Xinyuan-LilyGO/LilyGo-T-Relay/image/T-Relay8.jpg

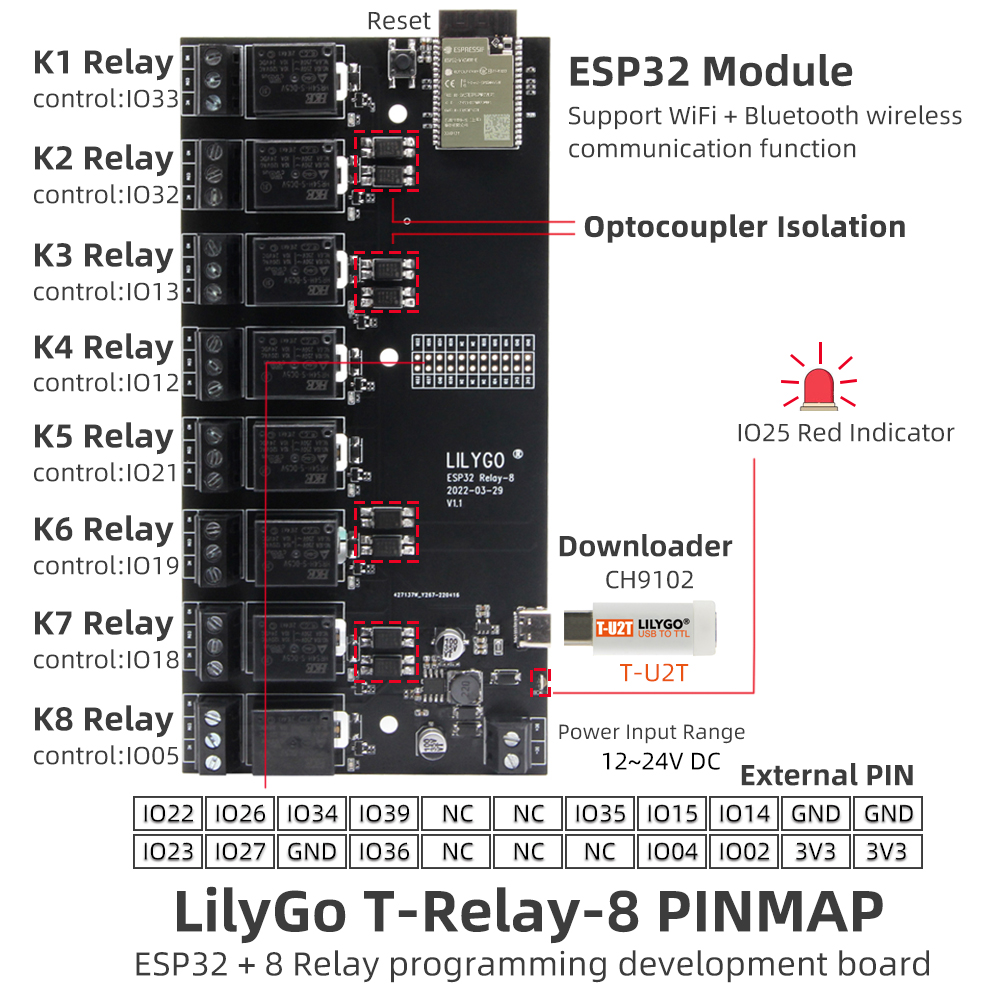
image/T-Relay8.jpg
