Xinyuan-LilyGO/LilyGo-T-Relay/examples/T-Relay-4-ESP32/w5500_esplib_v3.0/pin_config.h

/*
 * @Description: None
 * @version: None
 * @Author: None
 * @Date: 2023-06-05 13:01:59
 * @LastEditors: LILYGO_L
 * @LastEditTime: 2023-07-21 18:55:52
 */
#pragma once

/*ESP32S3*/
#define PIN_LCD_BL 38

#define PIN_LCD_D0 39
#define PIN_LCD_D1 40
#define PIN_LCD_D2 41
#define PIN_LCD_D3 42
#define PIN_LCD_D4 45
#define PIN_LCD_D5 46
#define PIN_LCD_D6 47
#define PIN_LCD_D7 48

#define PIN_POWER_ON 15

#define PIN_LCD_RES 5
#define PIN_LCD_CS 6
#define PIN_LCD_DC 7
#define PIN_LCD_WR 8
#define PIN_LCD_RD 9

#define PIN_BUTTON_1 0
#define PIN_BUTTON_2 14
#define PIN_BAT_VOLT 4

#define PIN_IIC_SCL 17
#define PIN_IIC_SDA 18

#define PIN_TOUCH_INT 16
#define PIN_TOUCH_RES 21

/* External expansion */
// SD
#define PIN_SD_CS 16
#define PIN_SD_CLK 21
#define PIN_SD_MISO 3
#define PIN_SD_MOSI 10

// MPR121_PIN
#define MPR121_ADDR1 0x5A
#define MPR121_ADDR2 0x5B // VCC
#define MPR121_IRQ_PIN 2
#define MPR121_SDA 18
#define MPR121_SCL 17

// PCF8575_PIN
#define T_DISPLAY_PCF8575_IIC_ADDRESS 0x20
#define PCF8575_IRQ_PIN 2
#define PCF8575_SDA 18
#define PCF8575_SCL 17
#define T_DISPLAY_PCF8575_INTERRUPTPIN 2

// PCM5102A_PIN
#define PCM5102A_LRCK 13
#define PCM5102A_DIN 12
#define PCM5102A_BCK 11

// XL95x5_PIN
#define T_DISPLAY_XL95x5_IIC_ADDRESS 0X20
#define T_DISPLAY_XL95x5_SDA 18 // Default configuration
#define T_DISPLAY_XL95x5_SCL 17
#define T_DISPLAY_XL95x5_INTERRUPTPIN 2

// W5500_PIN
#define PIN_W5500_CLK 22
#define PIN_W5500_MISO 13 // LilyGo-T-Relay-4
// #define PIN_W5500_MISO 34 // LilyGo-T-Relay-8
#define PIN_W5500_MOSI 26
#define PIN_W5500_CS 27
#define PIN_W5500_RESET 23
#define PIN_W5500_INT 36

// LilyGo-T-Relay-4
#define RELAY4_PIN_1 21
#define RELAY4_PIN_2 19
#define RELAY4_PIN_3 18
#define RELAY4_PIN_4 5
#define LED_PIN 25

// LilyGo-T-Relay-8
#define RELAY8_PIN_1 33
#define RELAY8_PIN_2 32
#define RELAY8_PIN_3 13
#define RELAY8_PIN_4 12
#define RELAY8_PIN_5 21
#define RELAY8_PIN_6 19
#define RELAY8_PIN_7 18
#define RELAY8_PIN_8 5
#define LED_PIN 25
