Xinyuan-LilyGO/LilyGo-T-Relay/examples/T-Relay-ESP32S3/NimBLE_Server/NimBLE_Server.ino

/**
 * @file      NimBLE_Server.ino
 * @author    Lewis He (lewishe@outlook.com)
 * @license   MIT
 * @copyright Copyright (c) 2023  Shenzhen Xin Yuan Electronic Technology Co., Ltd
 * @date      2023-02-27
 *
 */

#include <NimBLEDevice.h>
#include <ShiftRegister74HC595_NonTemplate.h>

#define DATA_PIN                    7
#define CLOCK_PIN                   5
#define LATCH_PIN                   6
#define ENABLE_PIN                  4       //EN Pin is only available in V1.1 version

ShiftRegister74HC595_NonTemplate *control = NULL;
static NimBLEServer *pServer;

/**  None of these are required as they will be handled by the library with defaults. **
 **                       Remove as you see fit for your needs                        */
class ServerCallbacks: public NimBLEServerCallbacks
{
    void onConnect(NimBLEServer *pServer)
    {
        Serial.println("Client connected");
        Serial.println("Multi-connect support: start advertising");
        NimBLEDevice::startAdvertising();
    };
    /** Alternative onConnect() method to extract details of the connection.
     *  See: src/ble_gap.h for the details of the ble_gap_conn_desc struct.
     */
    void onConnect(NimBLEServer *pServer, ble_gap_conn_desc *desc)
    {
        Serial.print("Client address: ");
        Serial.println(NimBLEAddress(desc->peer_ota_addr).toString().c_str());
        /** We can use the connection handle here to ask for different connection parameters.
         *  Args: connection handle, min connection interval, max connection interval
         *  latency, supervision timeout.
         *  Units; Min/Max Intervals: 1.25 millisecond increments.
         *  Latency: number of intervals allowed to skip.
         *  Timeout: 10 millisecond increments, try for 5x interval time for best results.
         */
        pServer->updateConnParams(desc->conn_handle, 24, 48, 0, 60);
    };
    void onDisconnect(NimBLEServer *pServer)
    {
        Serial.println("Client disconnected - start advertising");
        NimBLEDevice::startAdvertising();
    };
    void onMTUChange(uint16_t MTU, ble_gap_conn_desc *desc)
    {
        Serial.printf("MTU updated: %u for connection ID: %u\n", MTU, desc->conn_handle);
    };

    /********************* Security handled here **********************
    ****** Note: these are the same return values as defaults ********/
    uint32_t onPassKeyRequest()
    {
        Serial.println("Server Passkey Request");
        /** This should return a random 6 digit number for security
         *  or make your own static passkey as done here.
         */
        return 123456;
    };

    bool onConfirmPIN(uint32_t pass_key)
    {
        Serial.print("The passkey YES/NO number: "); Serial.println(pass_key);
        /** Return false if passkeys don't match. */
        return true;
    };

    void onAuthenticationComplete(ble_gap_conn_desc *desc)
    {
        /** Check that encryption was successful, if not we disconnect the client */
        if (!desc->sec_state.encrypted) {
            NimBLEDevice::getServer()->disconnect(desc->conn_handle);
            Serial.println("Encrypt connection failed - disconnecting client");
            return;
        }
        Serial.println("Starting BLE work!");
    };
};

/** Handler class for characteristic actions */
class CharacteristicCallbacks: public NimBLECharacteristicCallbacks
{
    void onRead(NimBLECharacteristic *pCharacteristic)
    {
        Serial.print(pCharacteristic->getUUID().toString().c_str());
        Serial.print(": onRead(), value: ");
        Serial.println(pCharacteristic->getValue().c_str());
    };


    /**
     *     BLE send data format:
     *
     *    |  Pin index          |  setValue  |
     *    |  Shift register pin |  value     |
     *
    */
    void onWrite(NimBLECharacteristic *pCharacteristic)
    {
        Serial.print(pCharacteristic->getUUID().toString().c_str());
        Serial.print(": onWrite(), value: ");
        Serial.println(pCharacteristic->getValue().c_str());
        if (pCharacteristic->getValue()) {
            const uint8_t *data = pCharacteristic->getValue().getValue(NULL);
            if (data && pCharacteristic->getValue().length() == 2) {
                Serial.print("Set Pin:"); Serial.print(data[0]); Serial.print(" to "); Serial.println(data[1]);
                control->set(data[0], data[1]);
            }
        }
    };

    /** Called before notification or indication is sent,
     *  the value can be changed here before sending if desired.
     */
    void onNotify(NimBLECharacteristic *pCharacteristic)
    {
        Serial.println("Sending notification to clients");
    };


    /** The status returned in status is defined in NimBLECharacteristic.h.
     *  The value returned in code is the NimBLE host return code.
     */
    void onStatus(NimBLECharacteristic *pCharacteristic, Status status, int code)
    {
        String str = ("Notification/Indication status code: ");
        str += status;
        str += ", return code: ";
        str += code;
        str += ", ";
        str += NimBLEUtils::returnCodeToString(code);
        Serial.println(str);
    };

    void onSubscribe(NimBLECharacteristic *pCharacteristic, ble_gap_conn_desc *desc, uint16_t subValue)
    {
        String str = "Client ID: ";
        str += desc->conn_handle;
        str += " Address: ";
        str += std::string(NimBLEAddress(desc->peer_ota_addr)).c_str();
        if (subValue == 0) {
            str += " Unsubscribed to ";
        } else if (subValue == 1) {
            str += " Subscribed to notfications for ";
        } else if (subValue == 2) {
            str += " Subscribed to indications for ";
        } else if (subValue == 3) {
            str += " Subscribed to notifications and indications for ";
        }
        str += std::string(pCharacteristic->getUUID()).c_str();

        Serial.println(str);
    };
};

/** Handler class for descriptor actions */
class DescriptorCallbacks : public NimBLEDescriptorCallbacks
{
    void onWrite(NimBLEDescriptor *pDescriptor)
    {
        std::string dscVal = pDescriptor->getValue();
        Serial.print("Descriptor witten value:");
        Serial.println(dscVal.c_str());
    };

    void onRead(NimBLEDescriptor *pDescriptor)
    {
        Serial.print(pDescriptor->getUUID().toString().c_str());
        Serial.println(" Descriptor read");
    };
};


/** Define callback instances globally to use for multiple Charateristics \ Descriptors */
static DescriptorCallbacks dscCallbacks;
static CharacteristicCallbacks chrCallbacks;


void setup()
{
    // EN Pin is only available in V1.1 version
    // Set Relay enable pin to output
    pinMode(ENABLE_PIN, OUTPUT);
    // Relay output enable pin disable
    digitalWrite(ENABLE_PIN, HIGH);

    Serial.begin(115200);

    Serial.println("Starting NimBLE Server");

    control = new ShiftRegister74HC595_NonTemplate(6, DATA_PIN, CLOCK_PIN, LATCH_PIN);
    assert(control);
    control->setAllLow();

    // Relay output enable pin enable
    digitalWrite(ENABLE_PIN, LOW);

    /** sets device name */
    NimBLEDevice::init("LilyGo-Relay");

    /** Optional: set the transmit power, default is 3db */
#ifdef ESP_PLATFORM
    NimBLEDevice::setPower(ESP_PWR_LVL_P9); /** +9db */
#else
    NimBLEDevice::setPower(9); /** +9db */
#endif

    /** Set the IO capabilities of the device, each option will trigger a different pairing method.
     *  BLE_HS_IO_DISPLAY_ONLY    - Passkey pairing
     *  BLE_HS_IO_DISPLAY_YESNO   - Numeric comparison pairing
     *  BLE_HS_IO_NO_INPUT_OUTPUT - DEFAULT setting - just works pairing
     */
    //NimBLEDevice::setSecurityIOCap(BLE_HS_IO_DISPLAY_ONLY); // use passkey
    //NimBLEDevice::setSecurityIOCap(BLE_HS_IO_DISPLAY_YESNO); //use numeric comparison

    /** 2 different ways to set security - both calls achieve the same result.
     *  no bonding, no man in the middle protection, secure connections.
     *
     *  These are the default values, only shown here for demonstration.
     */
    //NimBLEDevice::setSecurityAuth(false, false, true);
    // NimBLEDevice::setSecurityAuth(/*BLE_SM_PAIR_AUTHREQ_BOND | BLE_SM_PAIR_AUTHREQ_MITM |*/ BLE_SM_PAIR_AUTHREQ_SC);

    pServer = NimBLEDevice::createServer();
    pServer->setCallbacks(new ServerCallbacks());

    NimBLEService *pDeadService = pServer->createService("DEAD");
    NimBLECharacteristic *pBeefCharacteristic = pDeadService->createCharacteristic(
                "BEEF",
                NIMBLE_PROPERTY::READ |
                NIMBLE_PROPERTY::WRITE
            );

    pBeefCharacteristic->setCallbacks(&chrCallbacks);


    /** Start the services when finished creating all Characteristics and Descriptors */
    pDeadService->start();

    NimBLEAdvertising *pAdvertising = NimBLEDevice::getAdvertising();
    /** Add the services to the advertisment data **/
    pAdvertising->addServiceUUID(pDeadService->getUUID());

    /** If your device is battery powered you may consider setting scan response
     *  to false as it will extend battery life at the expense of less data sent.
     */
    pAdvertising->setScanResponse(true);
    pAdvertising->start();

    Serial.println("Advertising Started");
}


void loop()
{
    //no thing
}
