Xinyuan-LilyGO/LilyGo-T-Relay/examples/T-Relay-ESP32S3/RTC_DS3231_External_Module/RTC_DS3231_External_Module.ino

// Date and time functions using a DS3231 RTC connected via I2C and Wire lib
// @note DS3231 is an external RTC module, there is no DS3231 on T-Relay-S3,
// here only demonstrates how to use an external I2C device

#include "RTClib.h"
#include <Wire.h>

#define I2C_SDA   16
#define I2C_SCL   17

RTC_DS3231 rtc;

char daysOfTheWeek[7][12] = {"Sunday", "Monday", "Tuesday", "Wednesday", "Thursday", "Friday", "Saturday"};

void setup ()
{
    Serial.begin(115200);

    Wire.begin(I2C_SDA, I2C_SCL);

    if (! rtc.begin()) {
        Serial.println("Couldn't find RTC");
        while (1);
    }

    if (rtc.lostPower()) {
        Serial.println("RTC lost power, lets set the time!");
        // following line sets the RTC to the date & time this sketch was compiled
        rtc.adjust(DateTime(F(__DATE__), F(__TIME__)));
        // This line sets the RTC with an explicit date & time, for example to set
        // January 21, 2014 at 3am you would call:
        // rtc.adjust(DateTime(2014, 1, 21, 3, 0, 0));
    }
}

void loop ()
{
    DateTime now = rtc.now();

    Serial.print(now.year(), DEC);
    Serial.print('/');
    Serial.print(now.month(), DEC);
    Serial.print('/');
    Serial.print(now.day(), DEC);
    Serial.print(" (");
    Serial.print(daysOfTheWeek[now.dayOfTheWeek()]);
    Serial.print(") ");
    Serial.print(now.hour(), DEC);
    Serial.print(':');
    Serial.print(now.minute(), DEC);
    Serial.print(':');
    Serial.print(now.second(), DEC);
    Serial.println();

    Serial.print(" since midnight 1/1/1970 = ");
    Serial.print(now.unixtime());
    Serial.print("s = ");
    Serial.print(now.unixtime() / 86400L);
    Serial.println("d");

    // calculate a date which is 7 days and 30 seconds into the future
    DateTime future (now + TimeSpan(7, 12, 30, 6));

    Serial.print(" now + 7d + 30s: ");
    Serial.print(future.year(), DEC);
    Serial.print('/');
    Serial.print(future.month(), DEC);
    Serial.print('/');
    Serial.print(future.day(), DEC);
    Serial.print(' ');
    Serial.print(future.hour(), DEC);
    Serial.print(':');
    Serial.print(future.minute(), DEC);
    Serial.print(':');
    Serial.print(future.second(), DEC);
    Serial.println();

    Serial.print("Temperature: ");
    Serial.print(rtc.getTemperature());
    Serial.println(" C");

    Serial.println();
    delay(3000);
}
